cristianoag/microsdmapperv1/images/2023-06-09_18-23.jpg

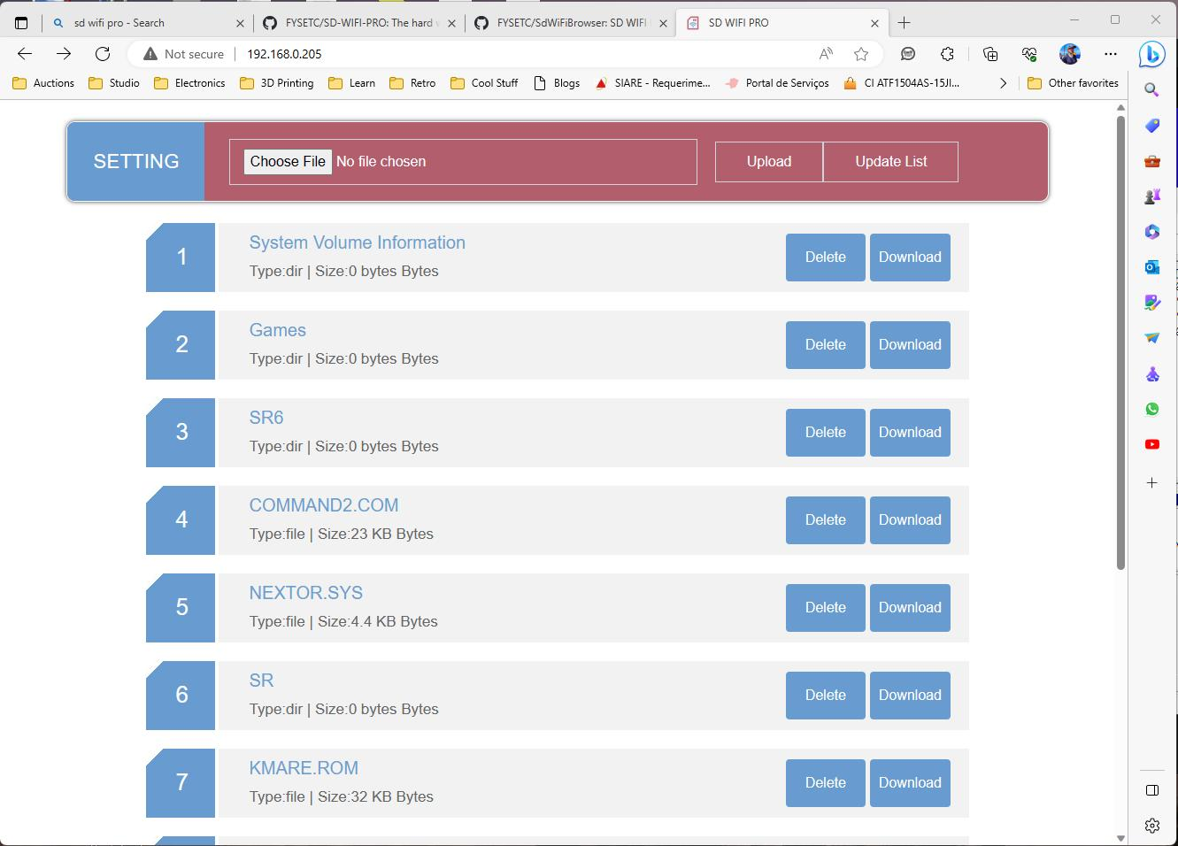
images/2023-06-09_18-23.jpg
