cristianoag/microsdmapperv1/hardware/microsdmapper_v1.2/microsdmapper.kicad_sch

## KiCad design hardware/microsdmapper_v1.2/microsdmapper.kicad_sch (2023-08-27)

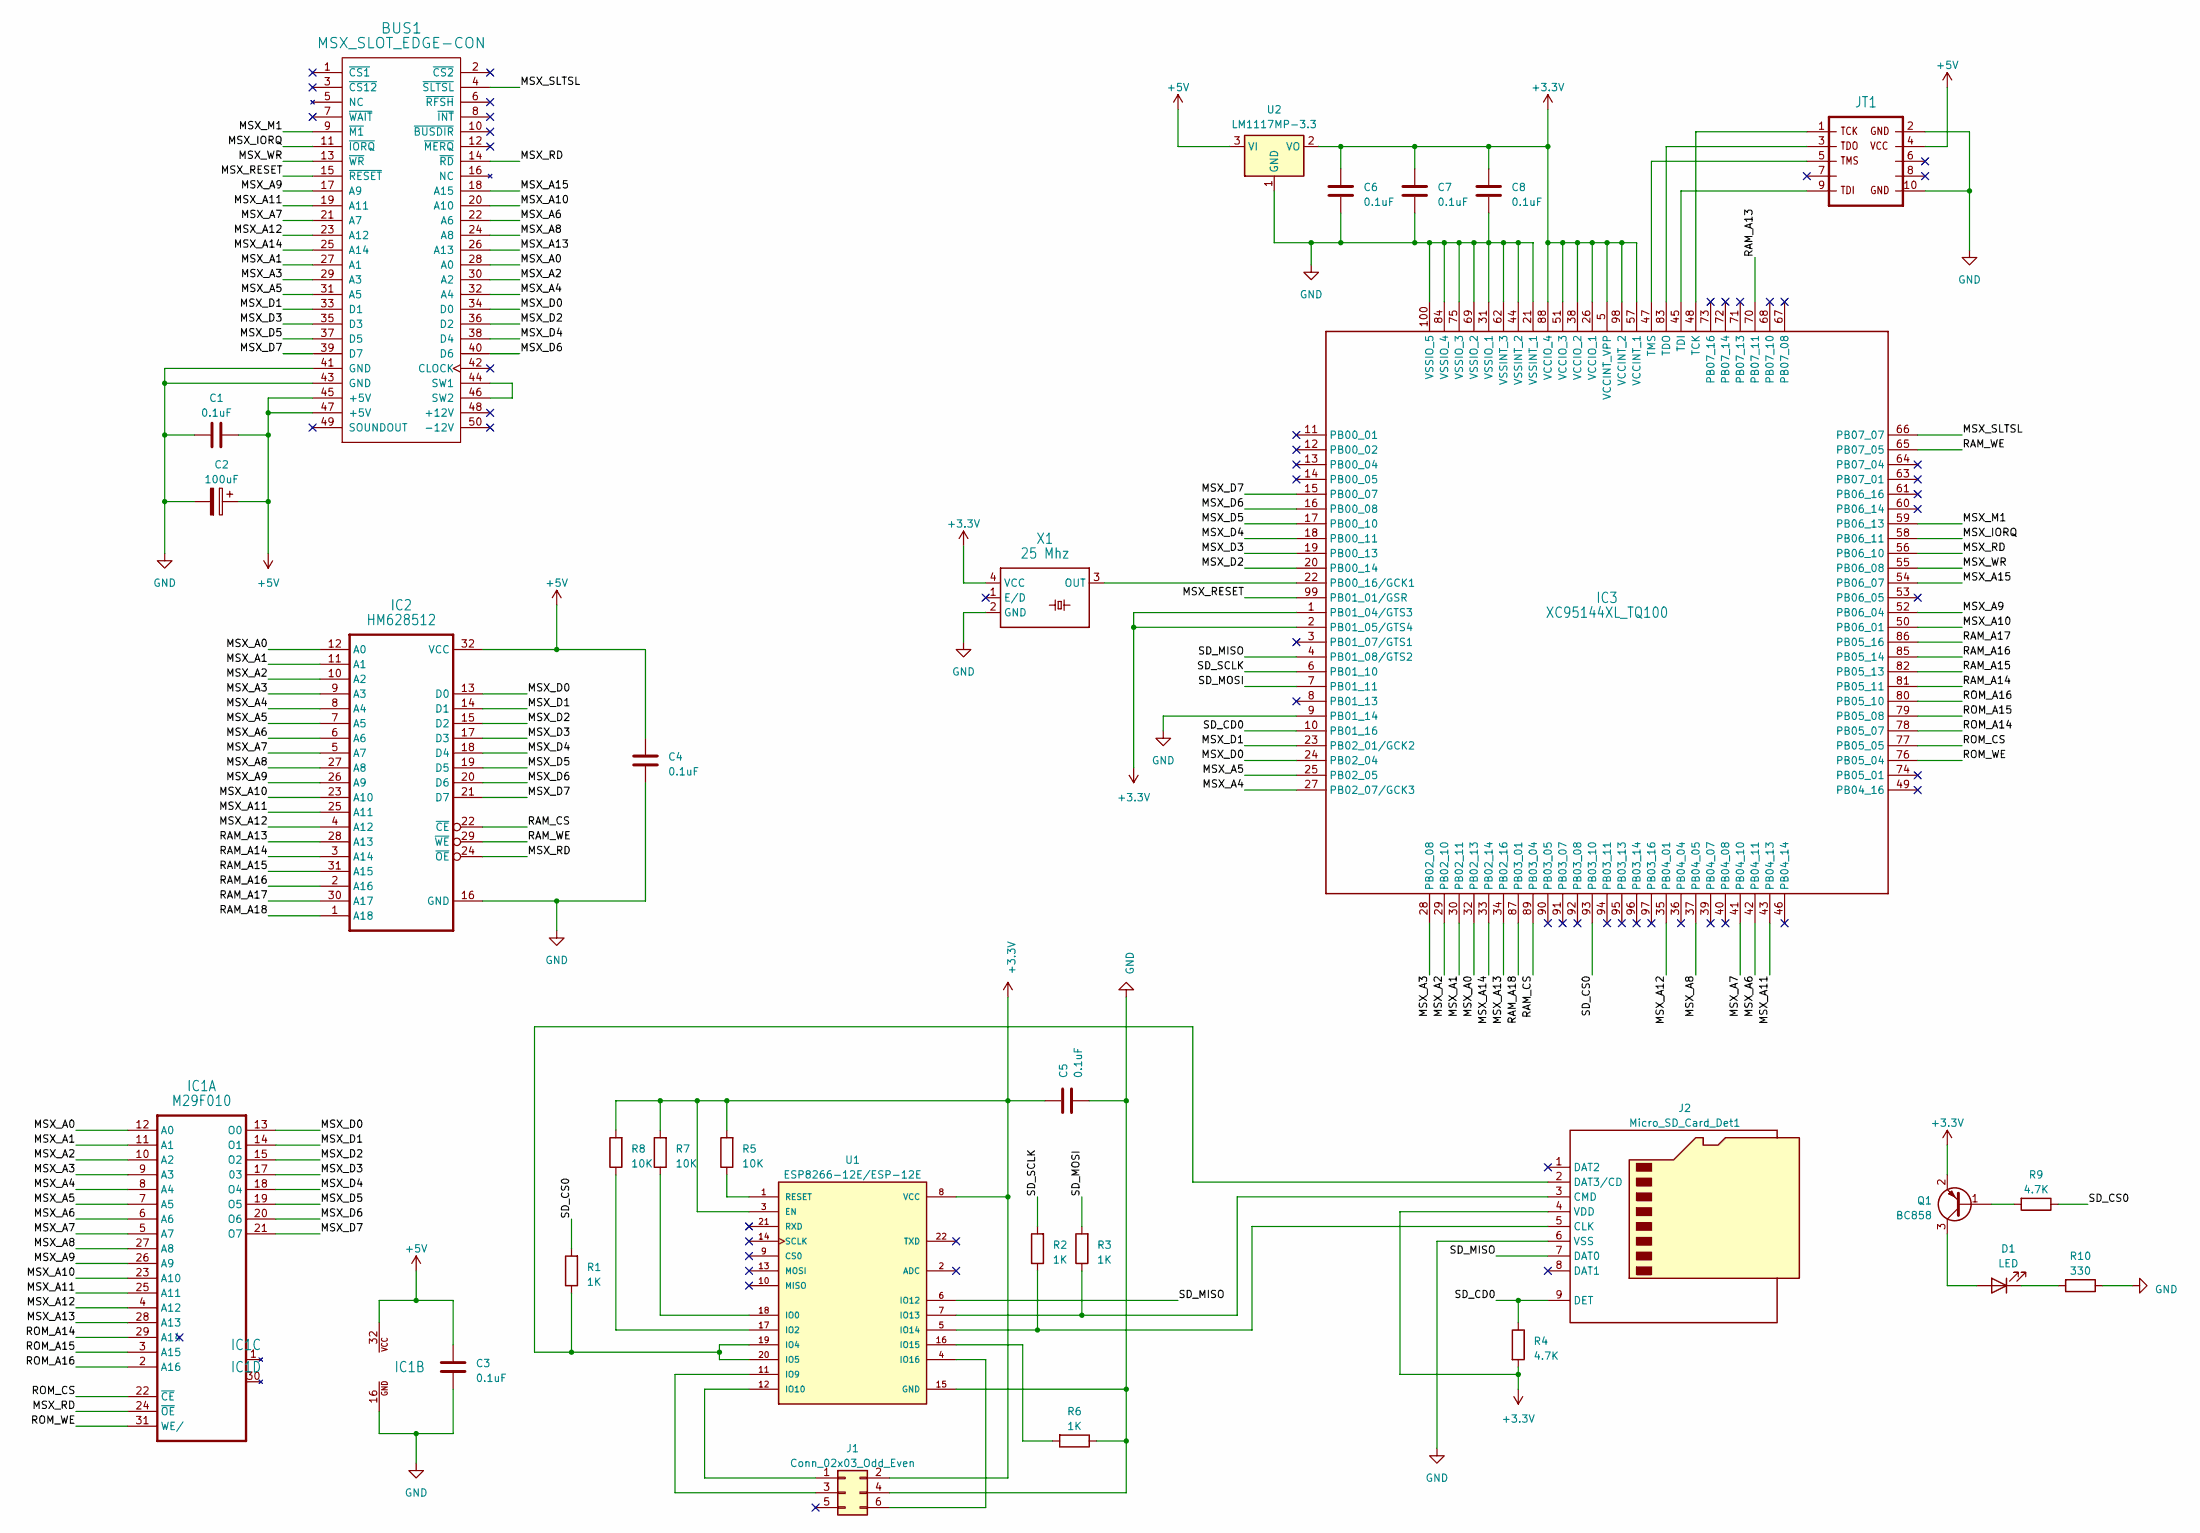
[picture p21: schematic microsdmapper.kicad_sch]

Parts:
BUS1: MSX_SLOT_EDGE-CON; msx_cartridge; MPN n/a
C1, C3, C4, C5, C6, C7, C8: 0.1uF; C_0603_1608Metric_Pad1.08x0.95mm_HandSolder
C2: 100uF; CP_Elec_5x4.5
D1: LED; LED_D3.0mm
IC1: M29F010; PLCC-32_11.4x14.0mm_P1.27mm
IC2: HM628512; SSOP-32_11.305x20.495mm_P1.27mm
IC3: XC95144XL_TQ100; VQFP-100_14x14mm_P0.5mm
J1: Conn_02x03_Odd_Even; PinHeader_2x03_P2.54mm_Vertical
J2: Micro_SD_Card_Det1; Conn_uSDcard
JT1: JTAG1A; PinHeader_2x05_P2.54mm_Vertical
Q1: BC858; SOT-23
R1, R2, R3, R6: 1K; R_0603_1608Metric_Pad0.98x0.95mm_HandSolder
R4, R9: 4.7K; R_0603_1608Metric_Pad0.98x0.95mm_HandSolder
R5, R7, R8: 10K; R_0603_1608Metric_Pad0.98x0.95mm_HandSolder
R10: 330; R_0603_1608Metric_Pad0.98x0.95mm_HandSolder
U1: ESP8266-12E/ESP-12E; XCVR_ESP8266-12E_ESP-12E
U2: LM1117MP-3.3; SOT-223-3_TabPin2
X1: 25 Mhz; Crystal_SMD_7050-4Pin_7.0x5.0mm

Connections:
+3.3V: C5.1, C6.1, C7.1, C8.1, IC3.1 (PB01_04/GTS3), IC3.2 (PB01_05/GTS4), IC3.5 (VCCINT_VPP), IC3.26 (VCCIO_1), IC3.38 (VCCIO_2), IC3.51 (VCCIO_3), IC3.57 (VCCINT_1), IC3.88 (VCCIO_4), IC3.98 (VCCINT_2), J1.2, J2.4 (VDD), Q1.2 (E), R4.2, R5.2, R7.2, R8.2, U1.3 (EN), U1.8 (VCC), U2.2 (VO), X1.4 (VCC)
+5V: BUS1.45 (+5V), BUS1.47 (+5V), C1.2, C2.1, C3.1, C4.1, IC1.32 (VCC), IC2.32 (VCC), JT1.4, U2.3 (VI)
GND: BUS1.41 (GND), BUS1.43 (GND), C1.1, C2.2, C3.2, C4.2, C5.2, C6.2, C7.2, C8.2, IC1.16 (GND), IC2.16 (GND), IC3.9 (PB01_14), IC3.21 (VSSINT_1), IC3.31 (VSSIO_1), IC3.44 (VSSINT_2), IC3.62 (VSSINT_3), IC3.69 (VSSIO_2), IC3.75 (VSSIO_3), IC3.84 (VSSIO_4), IC3.100 (VSSIO_5), J1.4, J2.6 (VSS), JT1.2, JT1.10, R6.1, R10.1, U1.15 (GND), U2.1 (GND), X1.2 (GND)
MSX_A0: BUS1.28 (A0), IC1.12 (A0), IC2.12 (A0), IC3.32 (PB02_13)
MSX_A1: BUS1.27 (A1), IC1.11 (A1), IC2.11 (A1), IC3.30 (PB02_11)
MSX_A2: BUS1.30 (A2), IC1.10 (A2), IC2.10 (A2), IC3.29 (PB02_10)
MSX_A3: BUS1.29 (A3), IC1.9 (A3), IC2.9 (A3), IC3.28 (PB02_08)
MSX_A4: BUS1.32 (A4), IC1.8 (A4), IC2.8 (A4), IC3.27 (PB02_07/GCK3)
MSX_A5: BUS1.31 (A5), IC1.7 (A5), IC2.7 (A5), IC3.25 (PB02_05)
MSX_A6: BUS1.22 (A6), IC1.6 (A6), IC2.6 (A6), IC3.42 (PB04_11)
MSX_A7: BUS1.21 (A7), IC1.5 (A7), IC2.5 (A7), IC3.41 (PB04_10)
MSX_A8: BUS1.24 (A8), IC1.27 (A8), IC2.27 (A8), IC3.37 (PB04_05)
MSX_A9: BUS1.17 (A9), IC1.26 (A9), IC2.26 (A9), IC3.52 (PB06_04)
MSX_A10: BUS1.20 (A10), IC1.23 (A10), IC2.23 (A10), IC3.50 (PB06_01)
MSX_A11: BUS1.19 (A11), IC1.25 (A11), IC2.25 (A11), IC3.43 (PB04_13)
MSX_A12: BUS1.23 (A12), IC1.4 (A12), IC2.4 (A12), IC3.35 (PB04_01)
MSX_A13: BUS1.26 (A13), IC1.28 (A13), IC3.34 (PB02_16)
MSX_A14: BUS1.25 (A14), IC3.33 (PB02_14)
MSX_A15: BUS1.18 (A15), IC3.54 (PB06_07)
MSX_D0: BUS1.34 (D0), IC1.13 (O0), IC2.13 (D0), IC3.24 (PB02_04)
MSX_D1: BUS1.33 (D1), IC1.14 (O1), IC2.14 (D1), IC3.23 (PB02_01/GCK2)
MSX_D2: BUS1.36 (D2~), IC1.15 (O2), IC2.15 (D2), IC3.20 (PB00_14)
MSX_D3: BUS1.35 (D3), IC1.17 (03), IC2.17 (D3), IC3.19 (PB00_13)
MSX_D4: BUS1.38 (D4), IC1.18 (O4), IC2.18 (D4), IC3.18 (PB00_11)
MSX_D5: BUS1.37 (D5), IC1.19 (O5), IC2.19 (D5), IC3.17 (PB00_10)
MSX_D6: BUS1.40 (D6), IC1.20 (O6), IC2.20 (D6), IC3.16 (PB00_08)
MSX_D7: BUS1.39 (D7), IC1.21 (O7), IC2.21 (D7), IC3.15 (PB00_07)
MSX_IORQ: BUS1.11 (~IORQ), IC3.58 (PB06_11)
MSX_M1: BUS1.9 (~M1), IC3.59 (PB06_13)
MSX_RD: BUS1.14 (~RD), IC1.24 (~OE), IC2.24 (~OE), IC3.56 (PB06_10)
MSX_RESET: BUS1.15 (~RESET), IC3.99 (PB01_01/GSR)
MSX_SLTSL: BUS1.4 (~SLTSL), IC3.66 (PB07_07)
MSX_WR: BUS1.13 (~WR), IC3.55 (PB06_08)
unnamed: BUS1.44 (SW1), BUS1.46 (SW2)
unnamed: D1.1 (K), R10.2
unnamed: D1.2 (A), Q1.3 (C)
unnamed: IC3.22 (PB00_16/GCK1), X1.3 (OUT)
unnamed: IC3.45 (TDI), JT1.9
unnamed: IC3.47 (TMS), JT1.5
unnamed: IC3.48 (TCK), JT1.1
unnamed: IC3.83 (TDO), JT1.3
unnamed: J1.1, U1.12 (IO10)
unnamed: J1.3, U1.11 (IO9)
unnamed: J1.6, U1.4 (IO16)
unnamed: J2.2 (DAT3/CD), R1.1, U1.19 (IO4), U1.20 (IO5)
unnamed: J2.3 (CMD), R3.1, U1.7 (IO13)
unnamed: J2.5 (CLK), R2.1, U1.5 (IO14)
unnamed: Q1.1 (B), R9.2
unnamed: R5.1, U1.1 (RESET)
unnamed: R6.2, U1.16 (IO15)
unnamed: R7.1, U1.18 (IO0)
unnamed: R8.1, U1.17 (IO2)
RAM_A13: IC2.28 (A13), IC3.70 (PB07_11)
RAM_A14: IC2.3 (A14), IC3.81 (PB05_11)
RAM_A15: IC2.31 (A15), IC3.82 (PB05_13)
RAM_A16: IC2.2 (A16), IC3.85 (PB05_14)
RAM_A17: IC2.30 (A17), IC3.86 (PB05_16)
RAM_A18: IC2.1 (A18), IC3.87 (PB03_01)
RAM_CS: IC2.22 (~CE), IC3.89 (PB03_04)
RAM_WE: IC2.29 (~WE), IC3.65 (PB07_05)
ROM_A14: IC1.29 (A14), IC3.78 (PB05_07)
ROM_A15: IC1.3 (A15), IC3.79 (PB05_08)
ROM_A16: IC1.2 (A16), IC3.80 (PB05_10)
ROM_CS: IC1.22 (~CE), IC3.77 (PB05_05)
ROM_WE: IC1.31 (WE/), IC3.76 (PB05_04)
SD_CD0: IC3.10 (PB01_16), J2.9 (DET), R4.1
SD_CS0: IC3.93 (PB03_10), R1.2, R9.1
SD_MISO: IC3.4 (PB01_08/GTS2), J2.7 (DAT0), U1.6 (IO12)
SD_MOSI: IC3.7 (PB01_11), R3.2
SD_SCLK: IC3.6 (PB01_10), R2.2
